pkropf/nerdyderby/nd-4.dxf

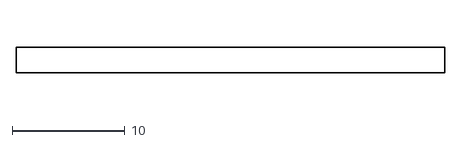
[picture p16: CAD file, 2014-07-16]
nd-4.dxf
38.0 x 2.25
