pkropf/nerdyderby/nd-11.dxf

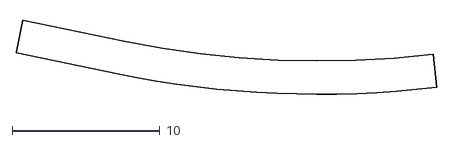
[picture p17: CAD file, 2014-07-16]
nd-11.dxf
28.5 x 5.40
