pkropf/nerdyderby/nd-12.dxf

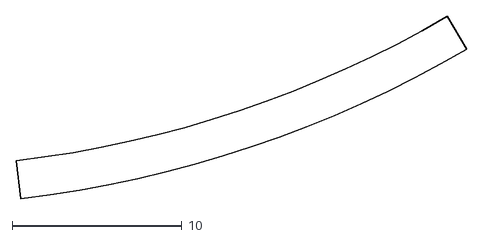
[picture p18: CAD file, 2014-07-16]
nd-12.dxf
26.6 x 10.7
