pkropf/nerdyderby/nd-a.dxf

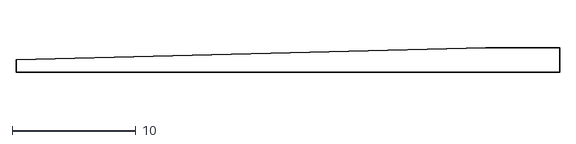
[picture p19: CAD file, 2014-07-16]
nd-a.dxf
44.0 x 2.00
