pkropf/nerdyderby/nd-9.dxf

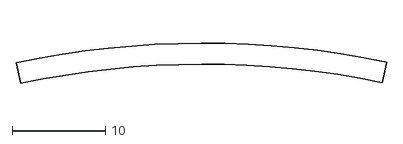
[picture p20: CAD file, 2014-07-16]
nd-9.dxf
39.7 x 5.02
