pkropf/nerdyderby/nd-c.dxf

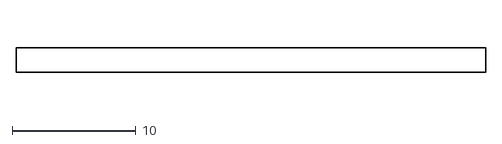
[picture p21: CAD file, 2014-07-16]
nd-c.dxf
38.0 x 2.00
