pkropf/nerdyderby/nd-gate.dxf

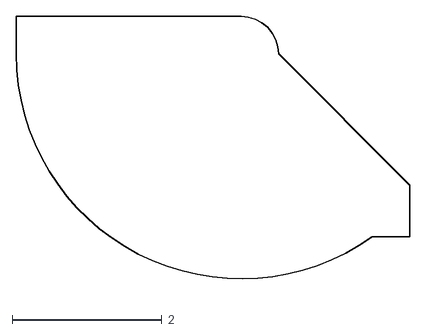
[picture p22: CAD file, 2014-07-16]
nd-gate.dxf
5.25 x 3.68
