pkropf/nerdyderby/nd-15.dxf

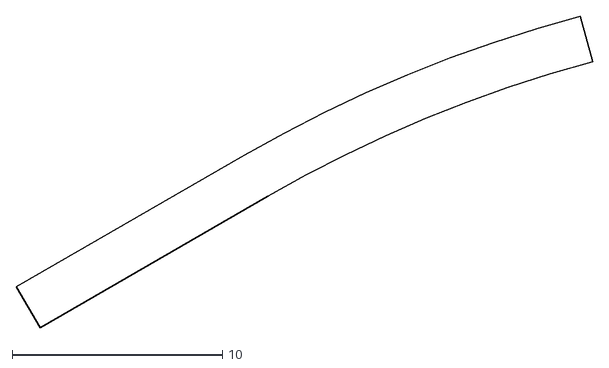
[picture p23: CAD file, 2014-07-16]
nd-15.dxf
27.4 x 14.8
