pkropf/nerdyderby/nd-m.dxf

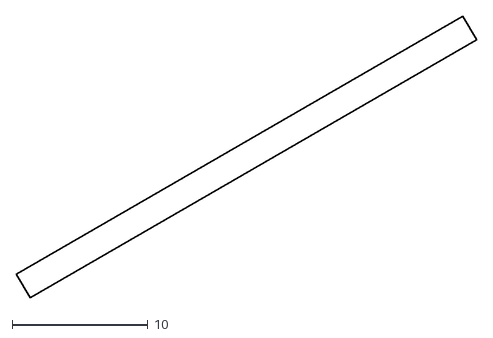
[picture p24: CAD file, 2014-07-16]
nd-m.dxf
33.8 x 20.7
