pkropf/nerdyderby/nd-i.dxf

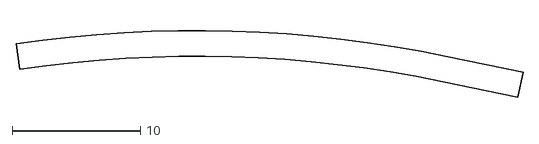
[picture p25: CAD file, 2014-07-16]
nd-i.dxf
39.6 x 5.83
