pkropf/nerdyderby/nd-7.dxf

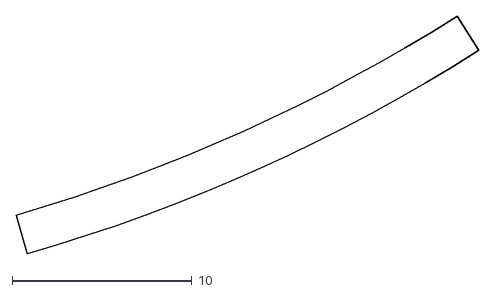
[picture p26: CAD file, 2014-07-16]
nd-7.dxf
25.8 x 13.2
