pkropf/nerdyderby/nd-17.dxf

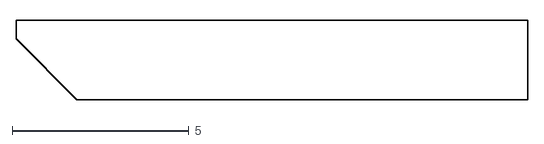
[picture p27: CAD file, 2014-07-16]
nd-17.dxf
14.5 x 2.25
