pkropf/nerdyderby/nd-g.dxf

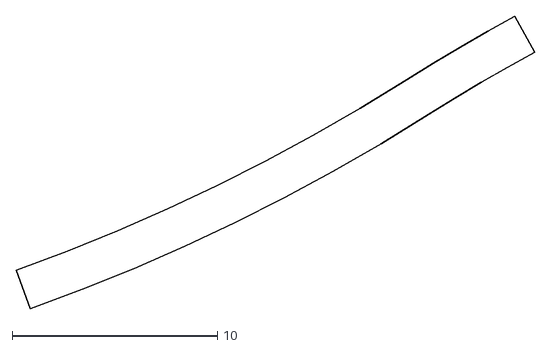
[picture p28: CAD file, 2014-07-16]
nd-g.dxf
25.3 x 14.3
