pkropf/nerdyderby/nd-6.dxf

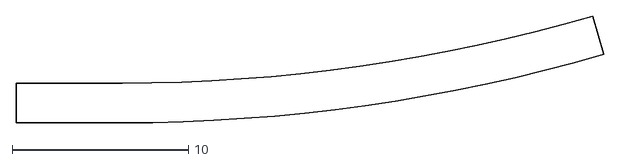
[picture p29: CAD file, 2014-07-16]
nd-6.dxf
33.3 x 6.04
