pkropf/nerdyderby/nd-3.dxf

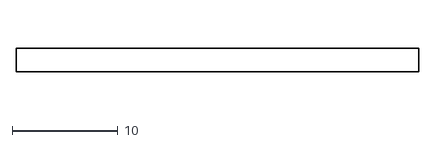
[picture p30: CAD file, 2014-07-16]
nd-3.dxf
38.0 x 2.25
