pkropf/nerdyderby/nd-j.dxf

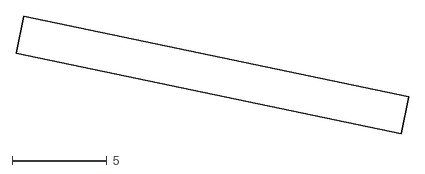
[picture p31: CAD file, 2014-07-16]
nd-j.dxf
20.7 x 6.19
