pkropf/nerdyderby/nd-e.dxf

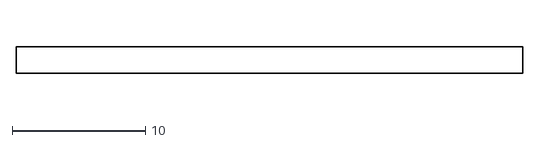
[picture p32: CAD file, 2014-07-16]
nd-e.dxf
38.0 x 2.00
