pkropf/nerdyderby/nd-1.dxf

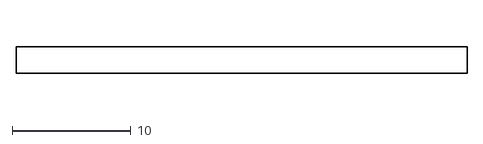
[picture p33: CAD file, 2014-07-16]
nd-1.dxf
38.0 x 2.25
