pkropf/nerdyderby/nd-l.dxf

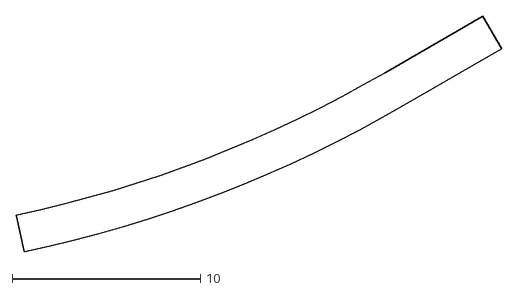
[picture p34: CAD file, 2014-07-16]
nd-l.dxf
25.8 x 12.5
