pkropf/nerdyderby/nd-13.dxf

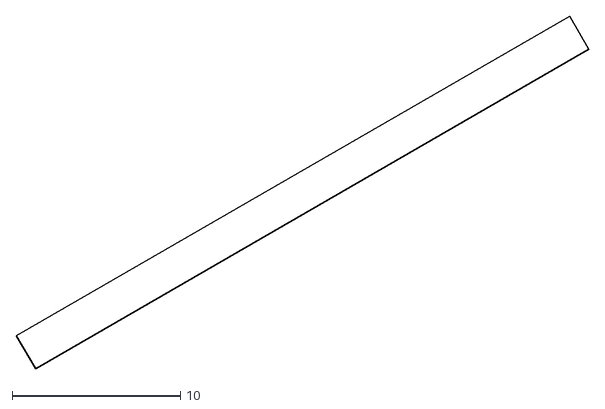
[picture p35: CAD file, 2014-07-16]
nd-13.dxf
34.0 x 20.9
